tebl/C64-Pi1541-Module/export/pcb_revision_a_preview.png

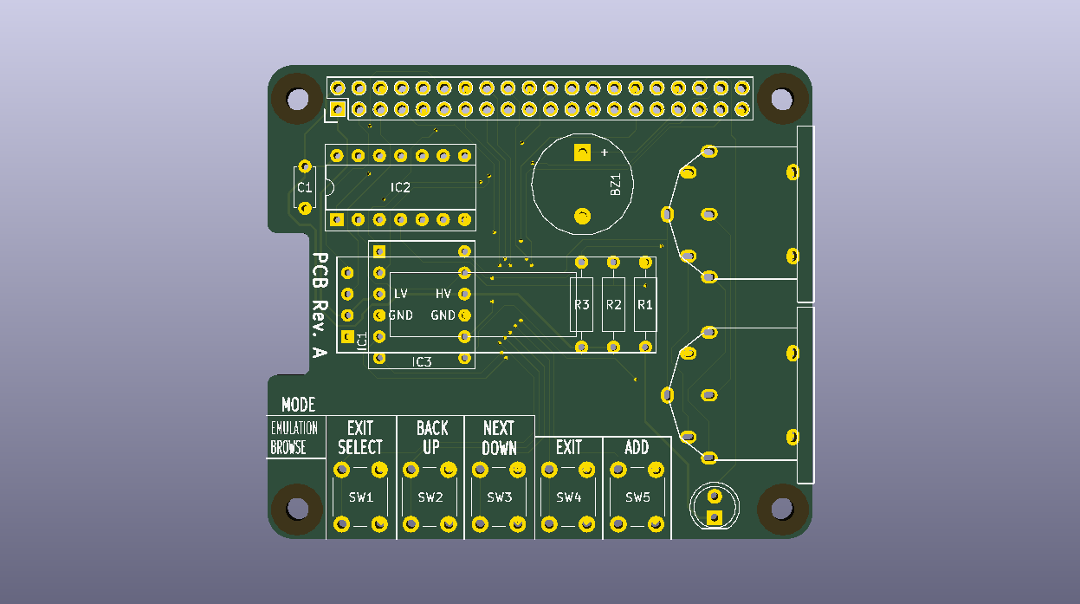
export/pcb_revision_a_preview.png
